Makerfabs/MaTouch_AMOLED_AI_CAMERA/example/test/pin_config.h

#pragma once

#define LCD_SDIO0 38
#define LCD_SDIO1 39
#define LCD_SDIO2 13
#define LCD_SDIO3 21
#define LCD_SCLK 40
#define LCD_CS 42
#define LCD_RST -1

#define LCD_WIDTH 368
#define LCD_HEIGHT 448

#define LCD_EN 14

// IIC
#define IIC_SDA 17
#define IIC_SCL 18

// TOUCH
#define TP_INT 48
#define TP_RST 47

// CAMERA
#define CAM_POWER_EN 46
#define CAM_PWDN -1
#define CAM_RESET -1
#define CAM_XCLK 4
#define CAM_SIOD 17
#define CAM_SIOC 18
#define CAM_Y2 9
#define CAM_Y3 11
#define CAM_Y4 12
#define CAM_Y5 10
#define CAM_Y6 8
#define CAM_Y7 6
#define CAM_Y8 5
#define CAM_Y9 3
#define CAM_VSYNC 1
#define CAM_HREF 2
#define CAM_PCLK 7

#define BUTTON_PIN 0
